AguaClara/PF200/Spring 2020/flowchannel_steelsleeve.png

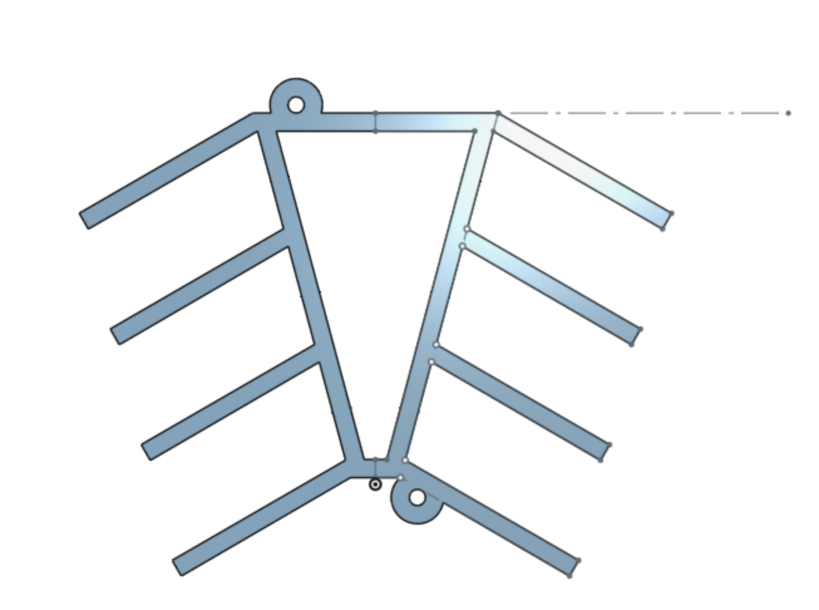
Spring 2020/flowchannel_steelsleeve.png
