AguaClara/PF200/Spring 2020/Image 11-4-19 at 7.04 PM.jpg

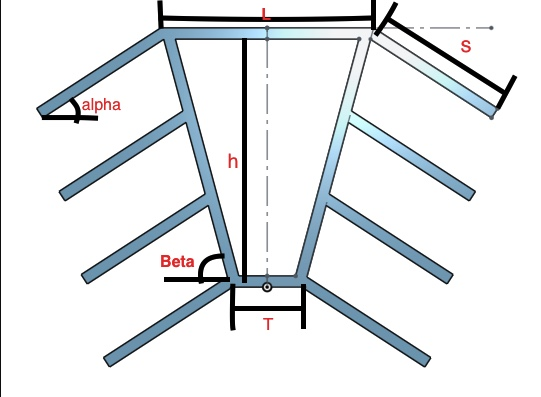
Spring 2020/Image 11-4-19 at 7.04 PM.jpg
