AguaClara/PF200/Spring 2020/Images/filter front.PNG

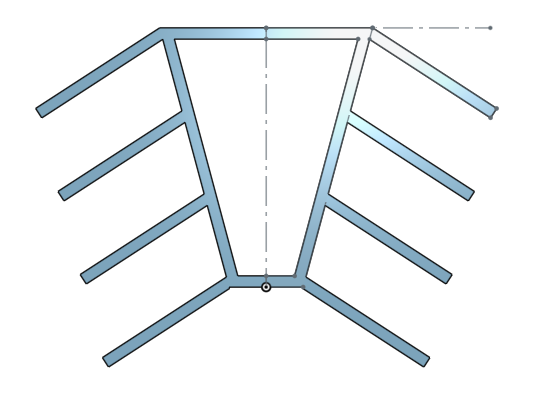
Spring 2020/Images/filter front.PNG
