AguaClara/PF200/Spring 2020/Images/filter isom.PNG

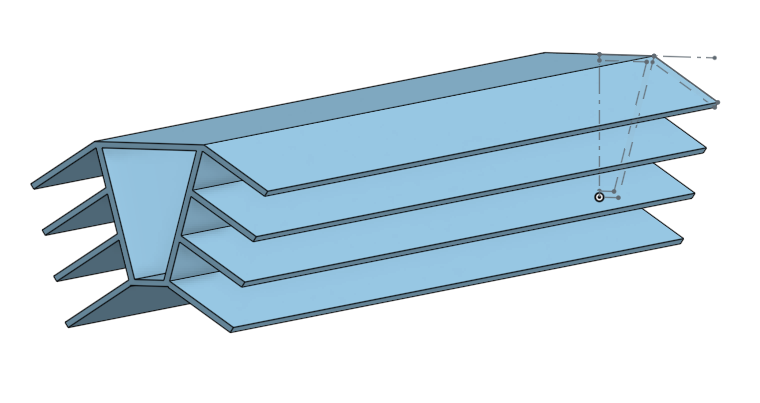
Spring 2020/Images/filter isom.PNG
