AguaClara/PF200/Spring 2020/Images/Flocculator.PNG

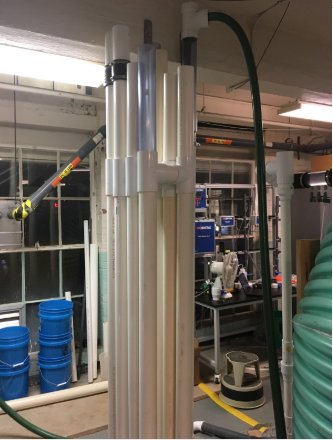
Spring 2020/Images/Flocculator.PNG
