AguaClara/PF200/Spring 2020/Images/IMG_0002.JPG

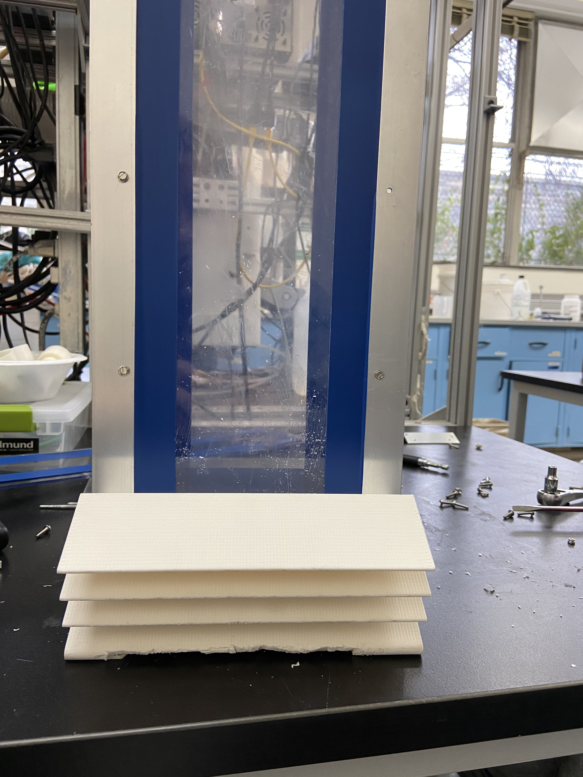
Spring 2020/Images/IMG_0002.JPG
