AguaClara/PF200/Spring 2021/Images/bending beam.png

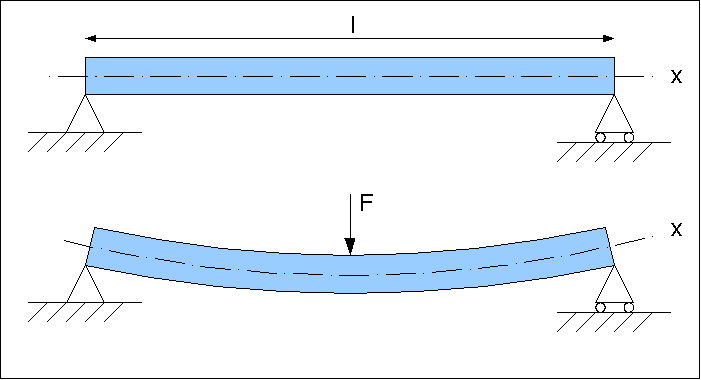
Spring 2021/Images/bending beam.png
