AguaClara/PF200/Spring 2021/Images/channels fitting into dado grooves.png

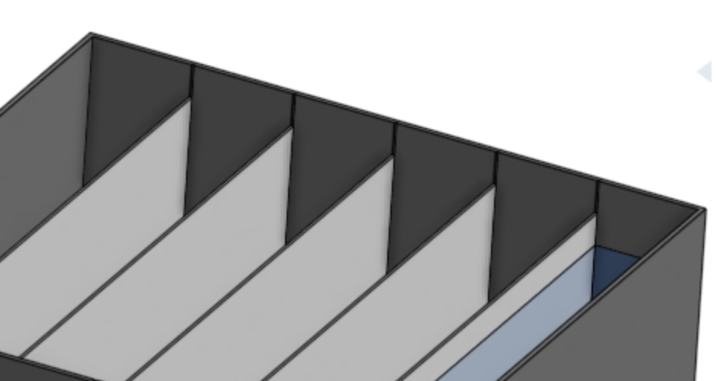
Spring 2021/Images/channels fitting into dado grooves.png
