AguaClara/PF200/Spring 2021/Images/Current Baffle.34.40 PM.png

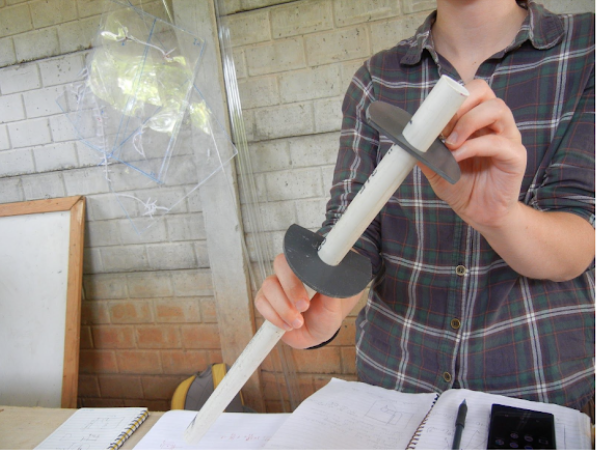
Spring 2021/Images/Current Baffle.34.40 PM.png
