AguaClara/PF200/Spring 2021/Images/dado grooves.png

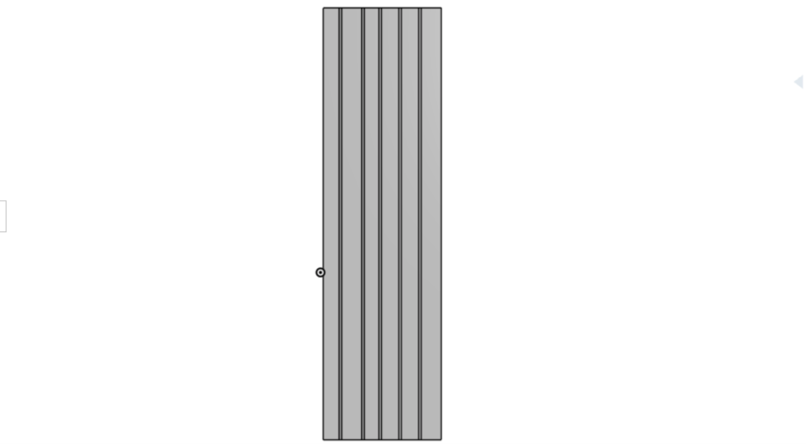
Spring 2021/Images/dado grooves.png
