AguaClara/PF200/Spring 2021/Images/external supports.png

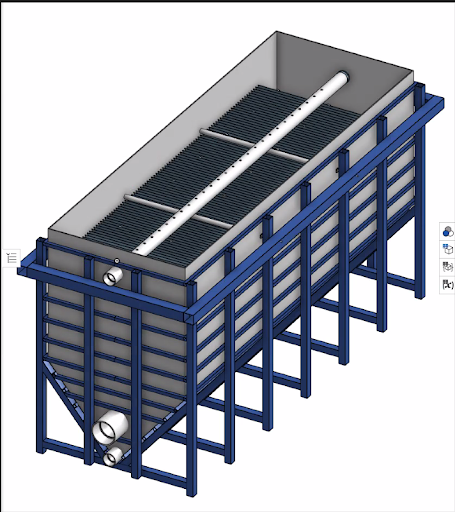
Spring 2021/Images/external supports.png
