AguaClara/PF200/Spring 2021/Images/Flocculator in Field.png

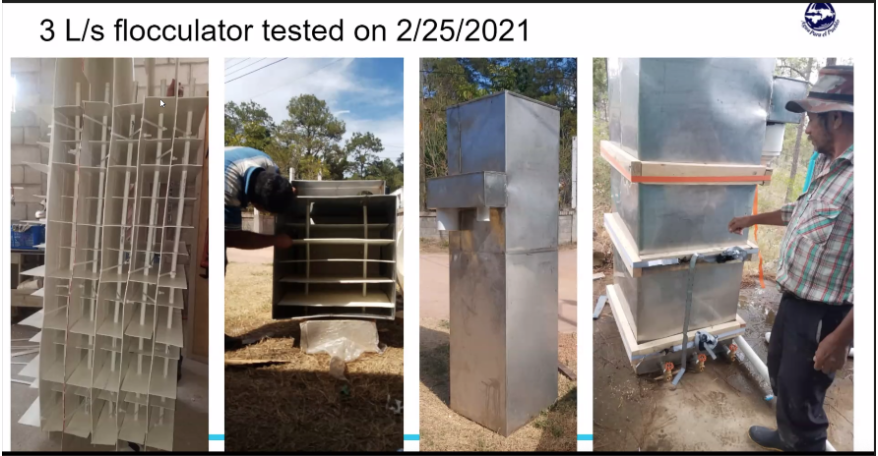
Spring 2021/Images/Flocculator in Field.png
