AguaClara/PF200/Spring 2021/Images/Flocculatorita Side.png

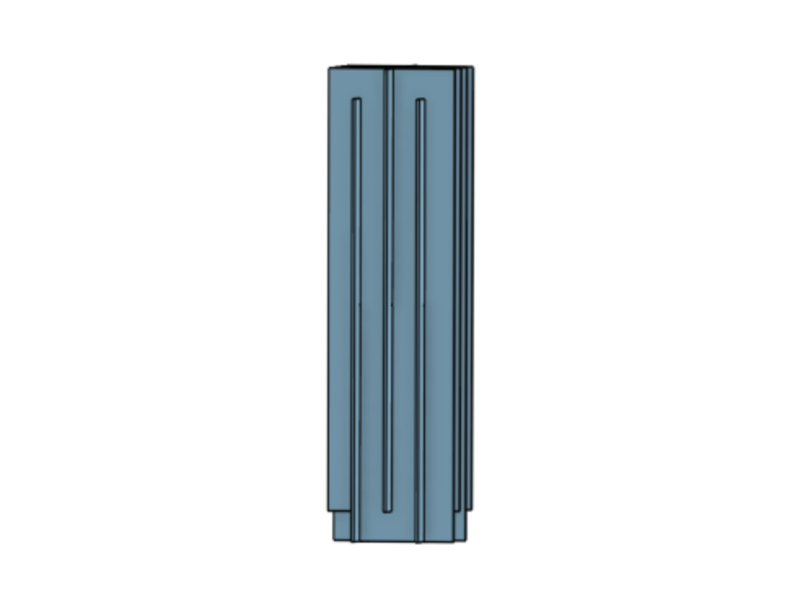
Spring 2021/Images/Flocculatorita Side.png
