AguaClara/PF200/Spring 2021/Images/Flocculatorita Top.png

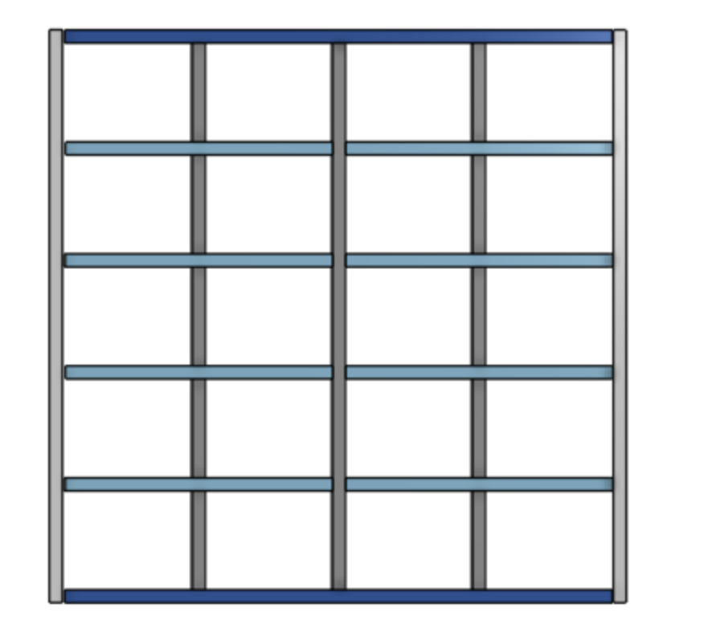
Spring 2021/Images/Flocculatorita Top.png
