AguaClara/PF200/Summer 2021/Images/IO Breakdown.png

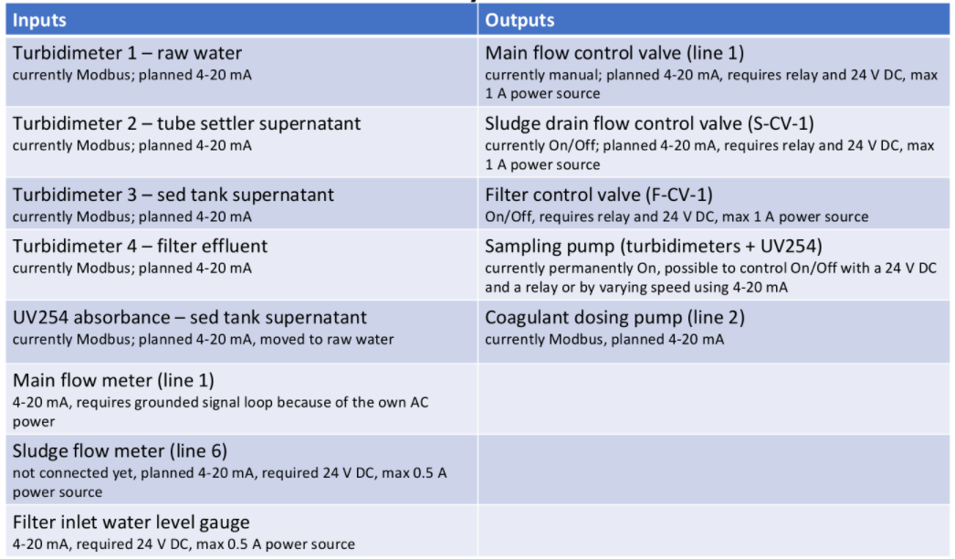
Summer 2021/Images/IO Breakdown.png
