AguaClara/PF200/Summer 2021/Images/Screenshot 2021-08-11 193538.png

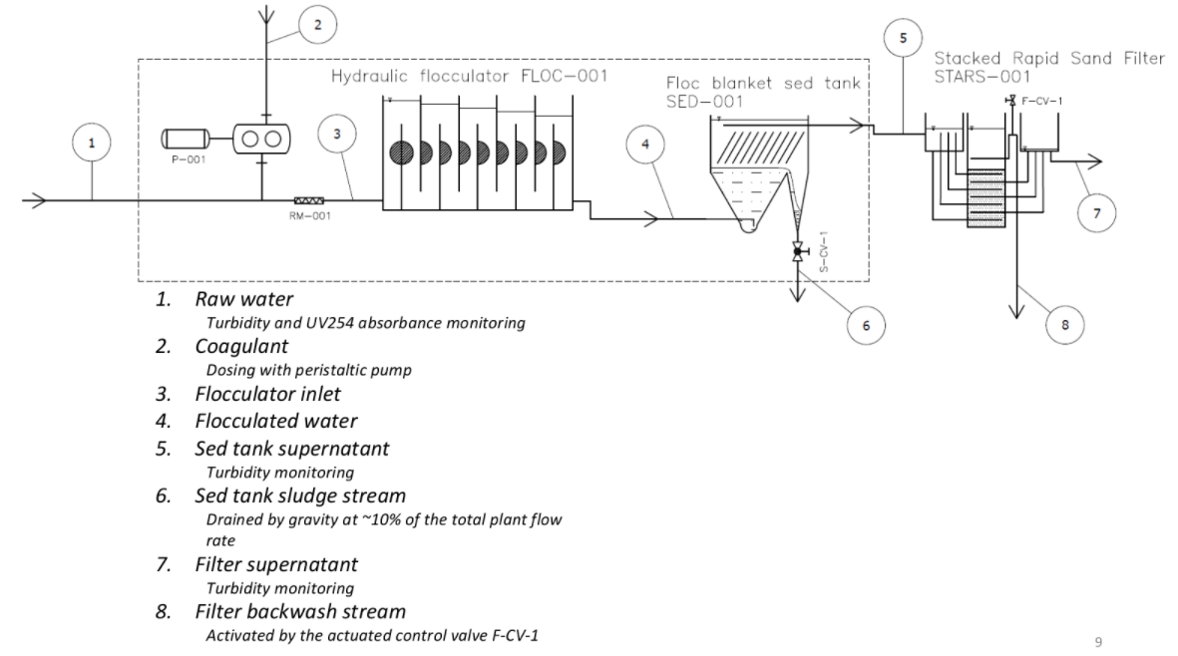
Summer 2021/Images/Screenshot 2021-08-11 193538.png
