AguaClara/PF200/Materials/rotoplast/foto cisterna 5,000 lts.JPG

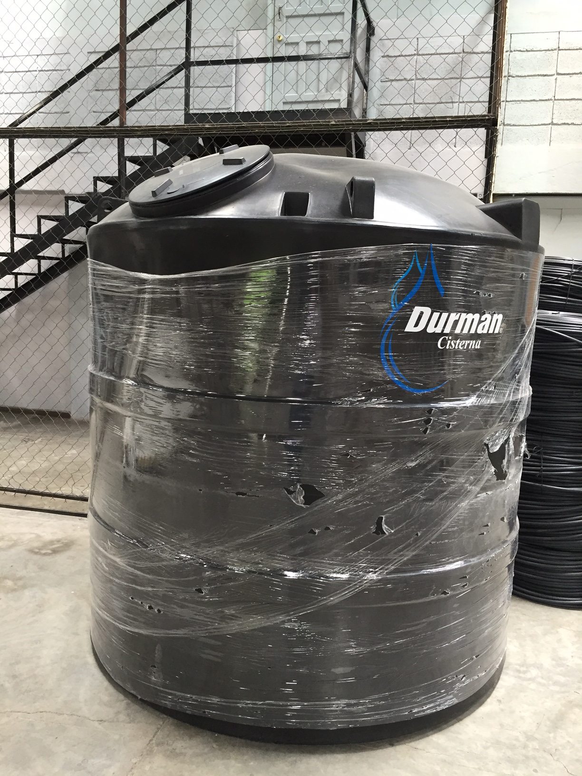
Materials/rotoplast/foto cisterna 5,000 lts.JPG
