AguaClara/PF200/Spring 2020/Images/pf200model.JPG

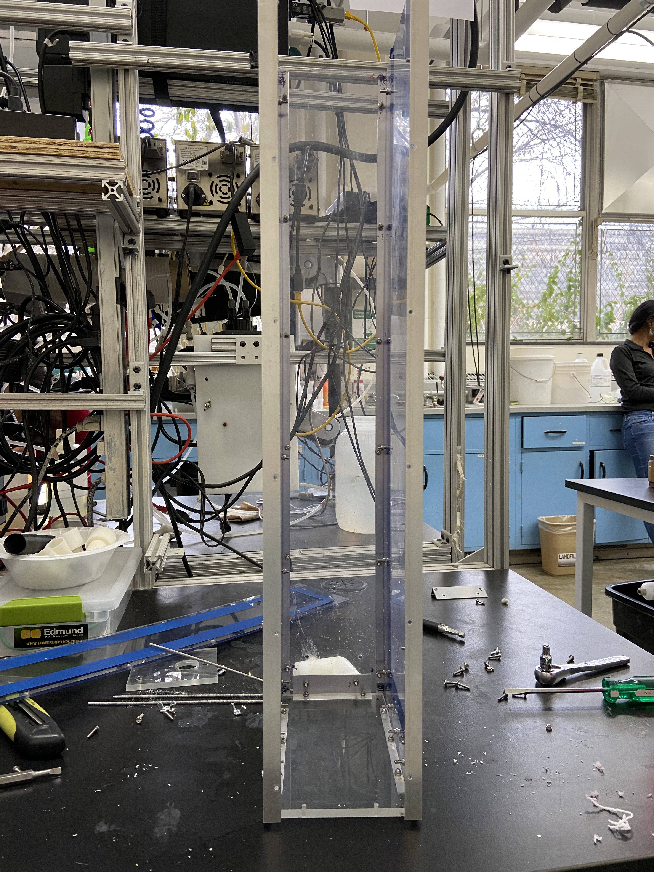
Spring 2020/Images/pf200model.JPG
